Manolo-BB/Sunrise-Simulator/Sunrise_simulator/Sunrise_simulator.kicad_sch

## KiCad design Sunrise_simulator/Sunrise_simulator.kicad_sch (2026-09-23, an earlier design)

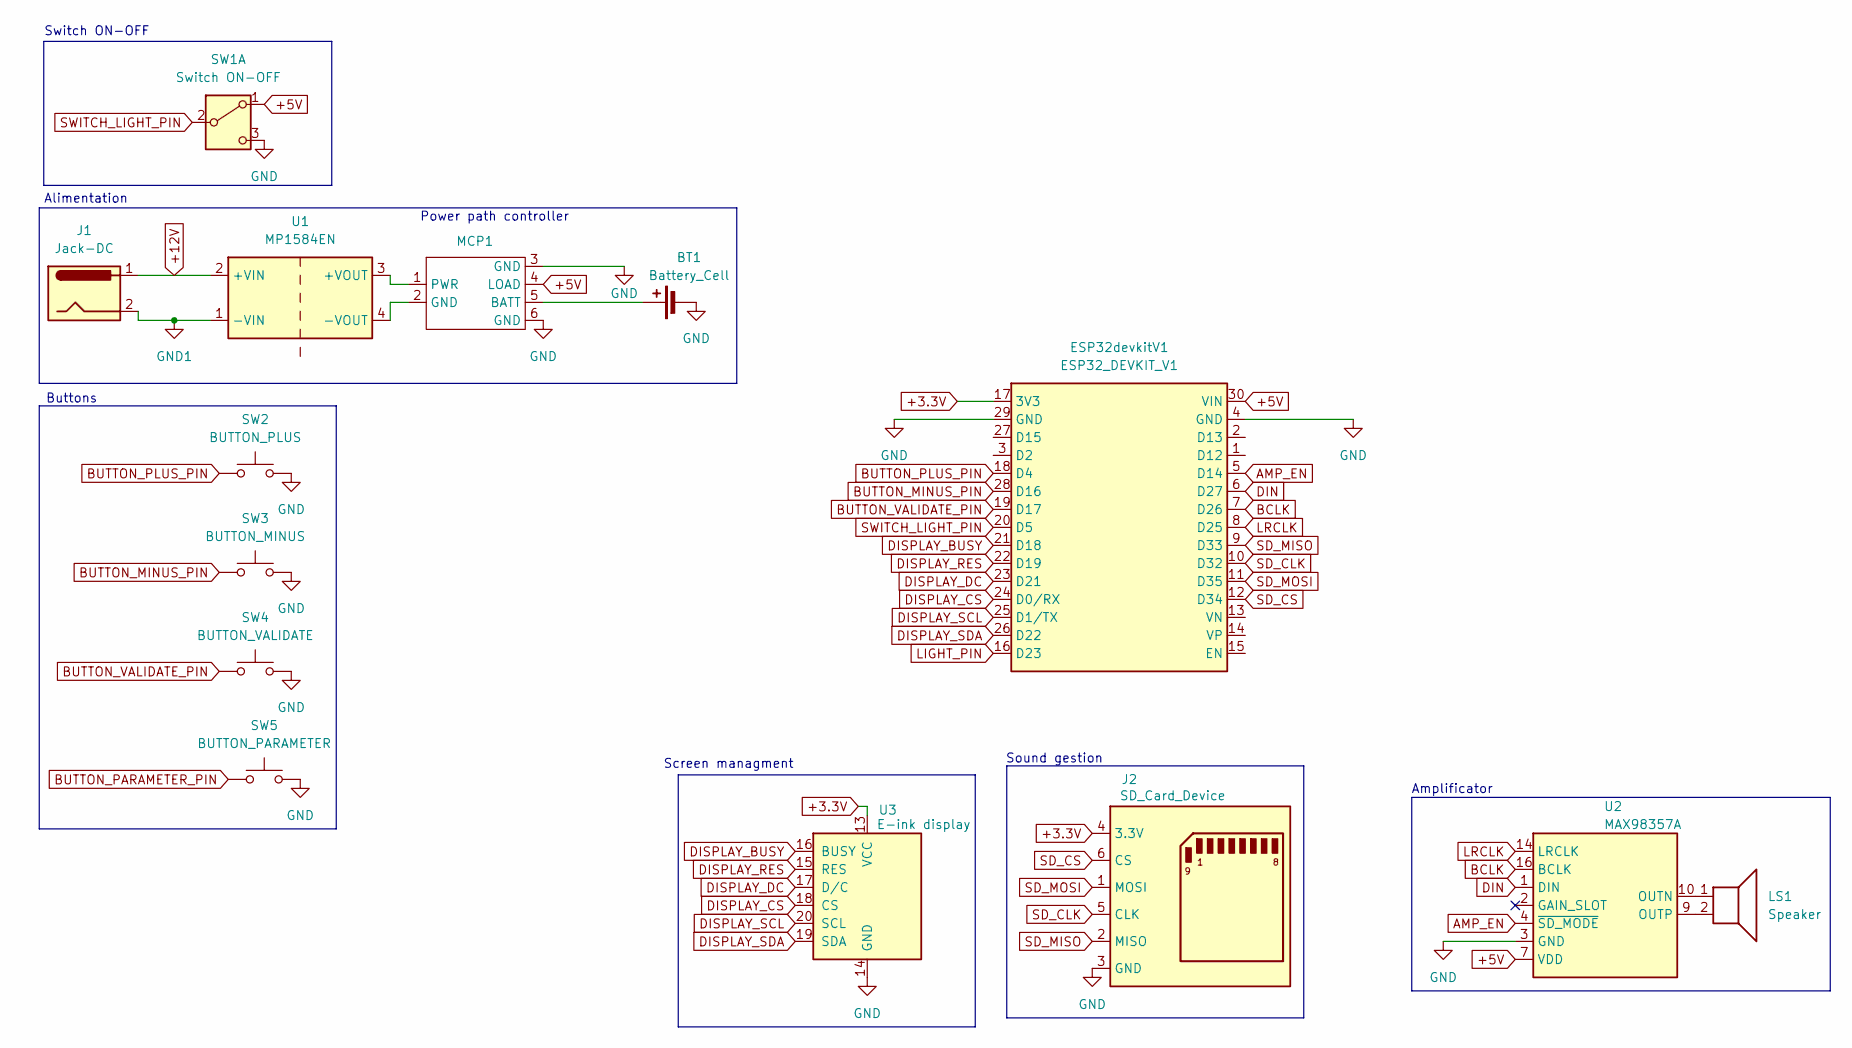
[picture p2: schematic Sunrise_simulator.kicad_sch]

Parts:
BT1: Battery_Cell
ESP32devkitV1: ESP32_DEVKIT_V1; Arduino_Nano
J1: Jack-DC
J2: SD_Card_Device
LS1: Speaker
MCP1: (no value)
SW1: Switch ON-OFF
SW2: BUTTON_PLUS
SW3: BUTTON_MINUS
SW4: BUTTON_VALIDATE
SW5: BUTTON_PARAMETER
U1: MP1584EN; Converter_DCDC_Murata_NCS1SxxxxSC_THT
U2: MAX98357A; TQFN-16-1EP_3x3mm_P0.5mm_EP1.23x1.23mm
U3: E-ink display; EA_DOGS104X-A

Connections:
+3.3V: ESP32devkitV1.17 (3V3), J2.4 (3.3V), U3.13 (VCC)
+5V: ESP32devkitV1.30 (VIN), MCP1.4 (LOAD), SW1.1 (A), U2.7 (VDD)
+12V: J1.1, U1.2 (+VIN)
AMP_EN: ESP32devkitV1.5 (D14), U2.4 (~SD_MODE)
BCLK: ESP32devkitV1.7 (D26), U2.16 (BCLK)
BUTTON_MINUS_PIN: ESP32devkitV1.28 (D16), SW3.1
BUTTON_PARAMETER_PIN: SW5.1
BUTTON_PLUS_PIN: ESP32devkitV1.18 (D4), SW2.1
BUTTON_VALIDATE_PIN: ESP32devkitV1.19 (D17), SW4.1
DIN: ESP32devkitV1.6 (D27), U2.1 (DIN)
DISPLAY_BUSY: ESP32devkitV1.21 (D18), U3.16 (BUSY)
DISPLAY_CS: ESP32devkitV1.24 (D0/RX), U3.18 (CS)
DISPLAY_DC: ESP32devkitV1.23 (D21), U3.17 (D/C)
DISPLAY_RES: ESP32devkitV1.22 (D19), U3.15 (RES)
DISPLAY_SCL: ESP32devkitV1.25 (D1/TX), U3.20 (SCL)
DISPLAY_SDA: ESP32devkitV1.26 (D22), U3.19 (SDA)
GND: BT1.2 (-), ESP32devkitV1.4 (GND), ESP32devkitV1.29 (GND), J2.3 (GND), MCP1.3 (GND), MCP1.6 (GND), SW1.3 (C), SW2.2, SW3.2, SW4.2, SW5.2, U2.3 (GND), U3.14 (GND)
GND1: J1.2, U1.1 (-VIN)
LIGHT_PIN: ESP32devkitV1.16 (D23)
LRCLK: ESP32devkitV1.8 (D25), U2.14 (LRCLK)
unnamed: BT1.1 (+), MCP1.5 (BATT)
unnamed: LS1.1, U2.10 (OUTN)
unnamed: LS1.2, U2.9 (OUTP)
unnamed: MCP1.1 (PWR), U1.3 (+VOUT)
unnamed: MCP1.2 (GND), U1.4 (-VOUT)
SD_CLK: ESP32devkitV1.10 (D32), J2.5 (CLK)
SD_CS: ESP32devkitV1.12 (D34), J2.6 (CS)
SD_MISO: ESP32devkitV1.9 (D33), J2.2 (MISO)
SD_MOSI: ESP32devkitV1.11 (D35), J2.1 (MOSI)
SWITCH_LIGHT_PIN: ESP32devkitV1.20 (D5), SW1.2 (B)

Notes on the sheet:
Alimentation
Power path controller
Screen managment
Amplificator
Switch ON-OFF
Sound gestion
Buttons
