Manolo-BB/Sunrise-Simulator/src/hardware/power.cpp

/*
POWER MANAGEMENT

This file contains the implementation of power management functions for the hardware 
 like functions allowing to switch various power sources on and off and deepsleep functionality.
 
 */ 
